MUDAL/Domestic-energy-monitoring-system/Schematic/Energy_Monitor/Energy_Monitor.kicad_sch

## KiCad design Schematic/Energy_Monitor/Energy_Monitor.kicad_sch (2023-05-23, an earlier design)

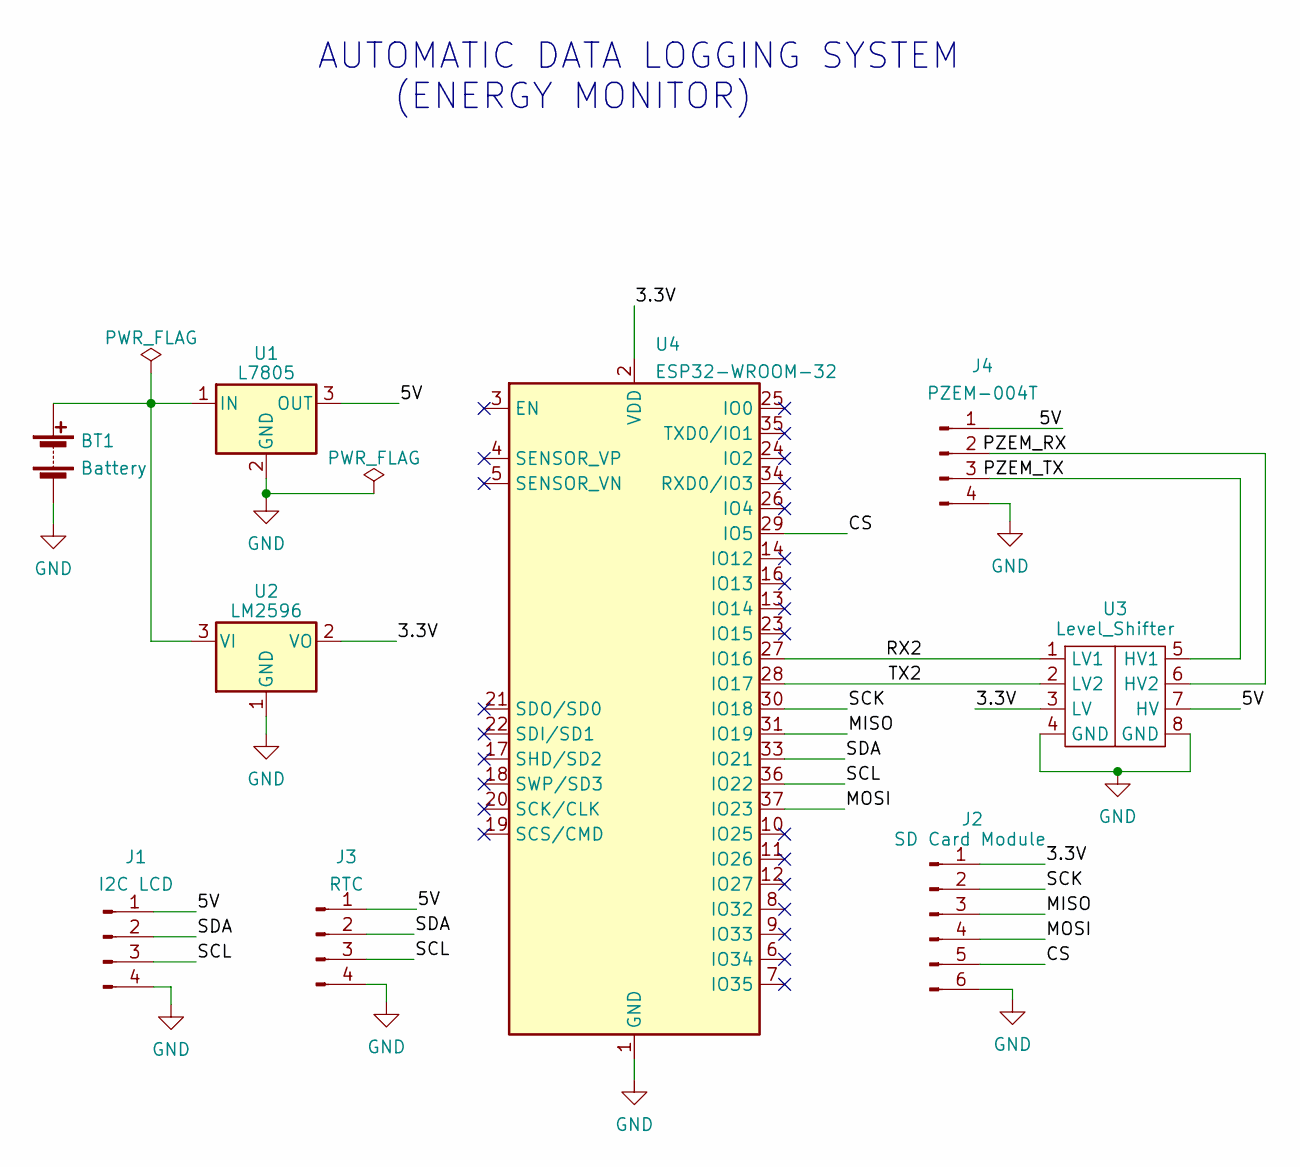
[picture p4: schematic Energy_Monitor.kicad_sch]

Parts:
BT1: Battery
J1: I2C LCD
J2: SD Card Module
J3: RTC
J4: PZEM-004T
U1: L7805
U2: LM2596
U3: Level_Shifter
U4: ESP32-WROOM-32

Connections:
3.3V: J2.1, U2.2 (VO), U3.3 (LV), U4.2 (VDD)
5V: J1.1, J3.1, J4.1, U1.3 (OUT), U3.7 (HV)
CS: J2.5, U4.29 (IO5)
GND: BT1.2 (-), J1.4, J2.6, J3.4, J4.4, U1.2 (GND), U2.1 (GND), U3.4 (GND), U3.8 (GND), U4.1 (GND), U4.15 (GND), U4.38 (GND), U4.39 (GND)
MISO: J2.3, U4.31 (IO19)
MOSI: J2.4, U4.37 (IO23)
unnamed: BT1.1 (+), U1.1 (IN), U2.3 (VI)
PZEM_RX: J4.2, U3.6 (HV2)
PZEM_TX: J4.3, U3.5 (HV1)
RX2: U3.1 (LV1), U4.27 (IO16)
SCK: J2.2, U4.30 (IO18)
SCL: J1.3, J3.3, U4.36 (IO22)
SDA: J1.2, J3.2, U4.33 (IO21)
TX2: U3.2 (LV2), U4.28 (IO17)

Notes on the sheet:
AUTOMATIC DATA LOGGING SYSTEM (ENERGY MONITOR)
